torbers/shepherd_mix/brand/kh-24eva1117.png

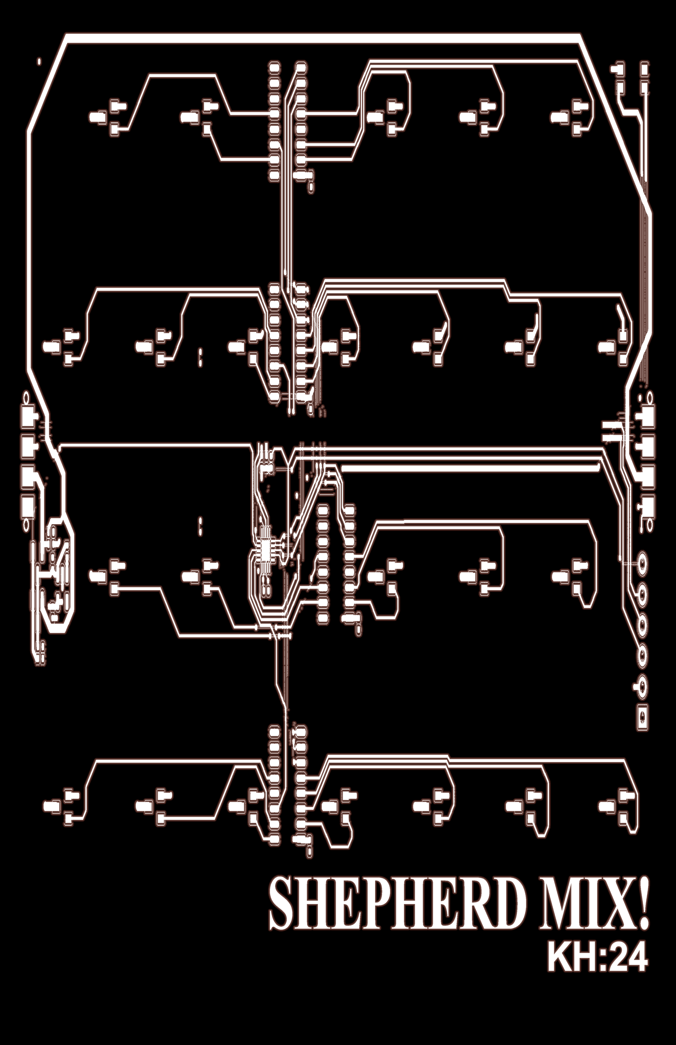
brand/kh-24eva1117.png
