torbers/shepherd_mix/brand/kh-24eva1117_v_one.png

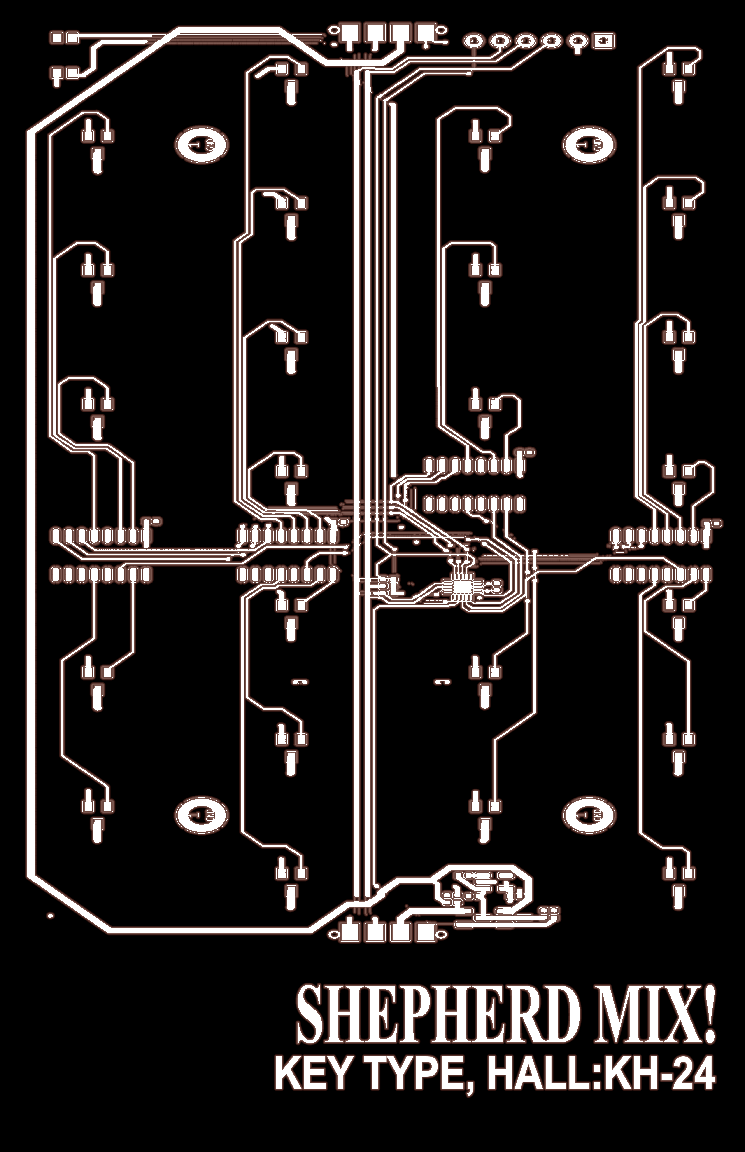
brand/kh-24eva1117_v_one.png
