torbers/shepherd_mix/brand/xray/1.jpg

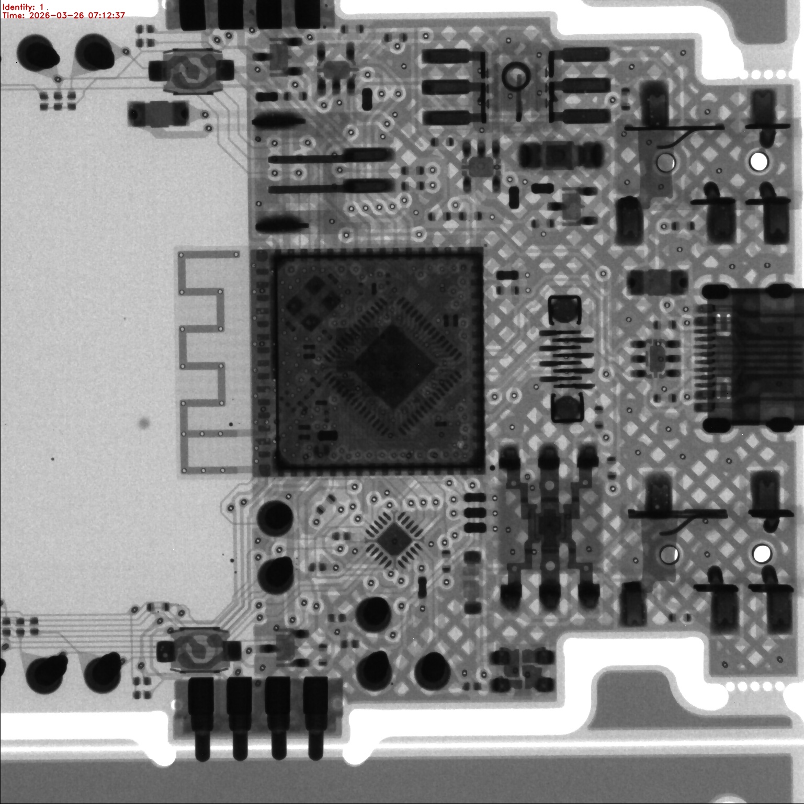
brand/xray/1.jpg
