torbers/shepherd_mix/brand/xray/2.jpg

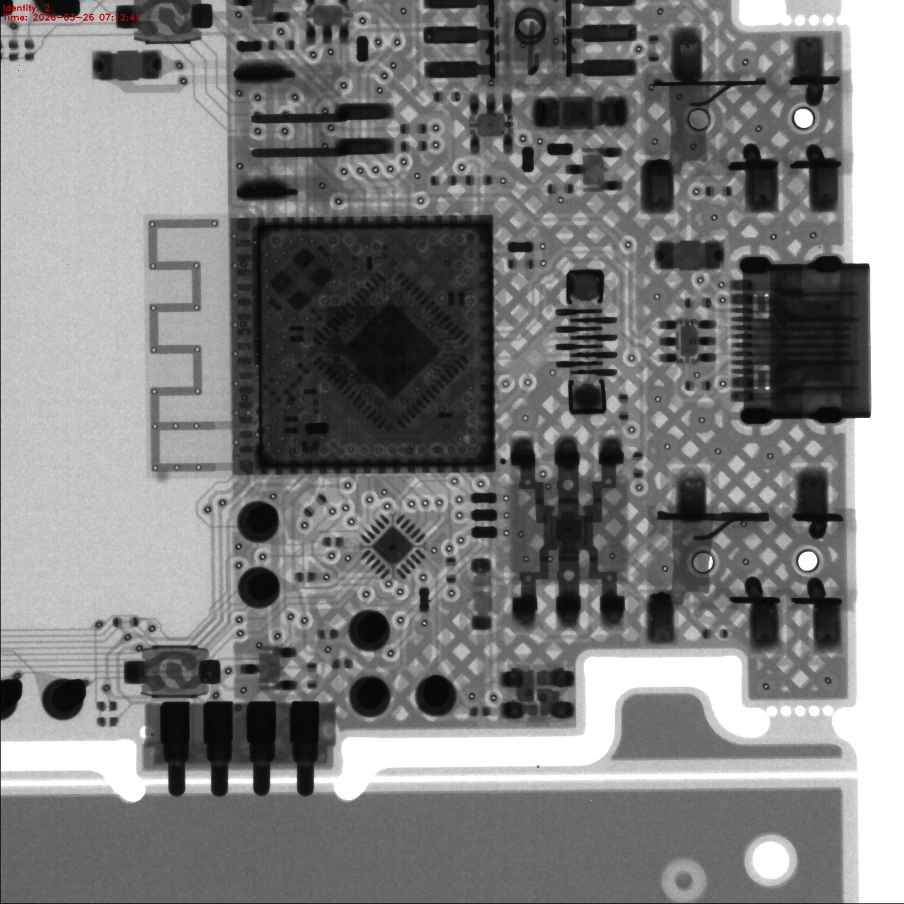
brand/xray/2.jpg
