torbers/shepherd_mix/brand/xray/5.jpg

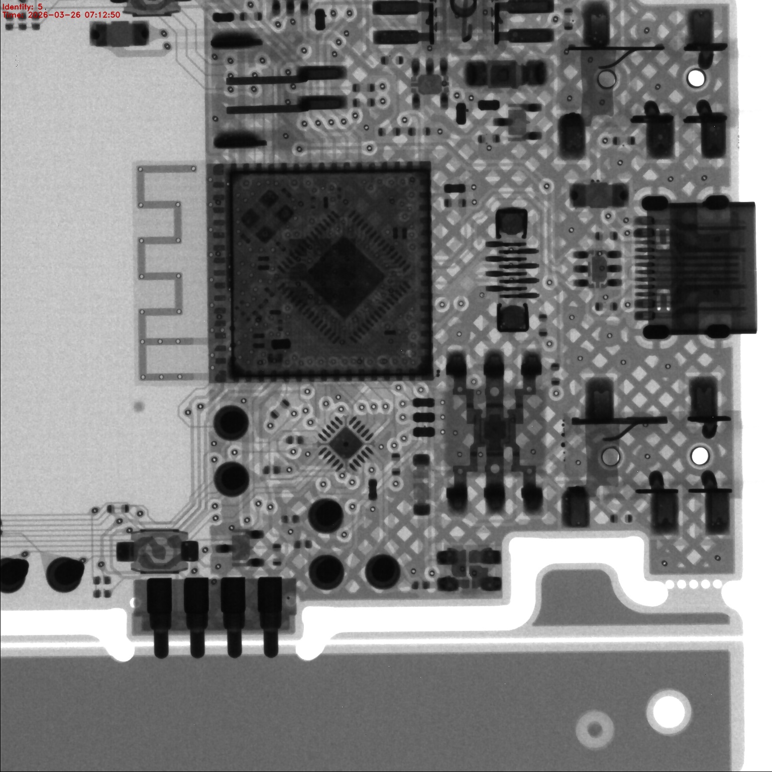
brand/xray/5.jpg
