torbers/shepherd_mix/kh-24 hall/hall face/ogd.png

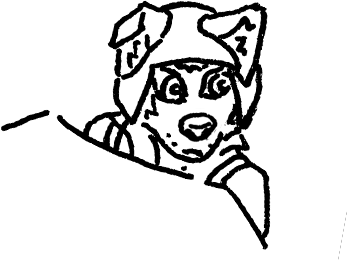
kh-24 hall/hall face/ogd.png
