torbers/shepherd_mix/kh-24 hall/hall_main_front2.png

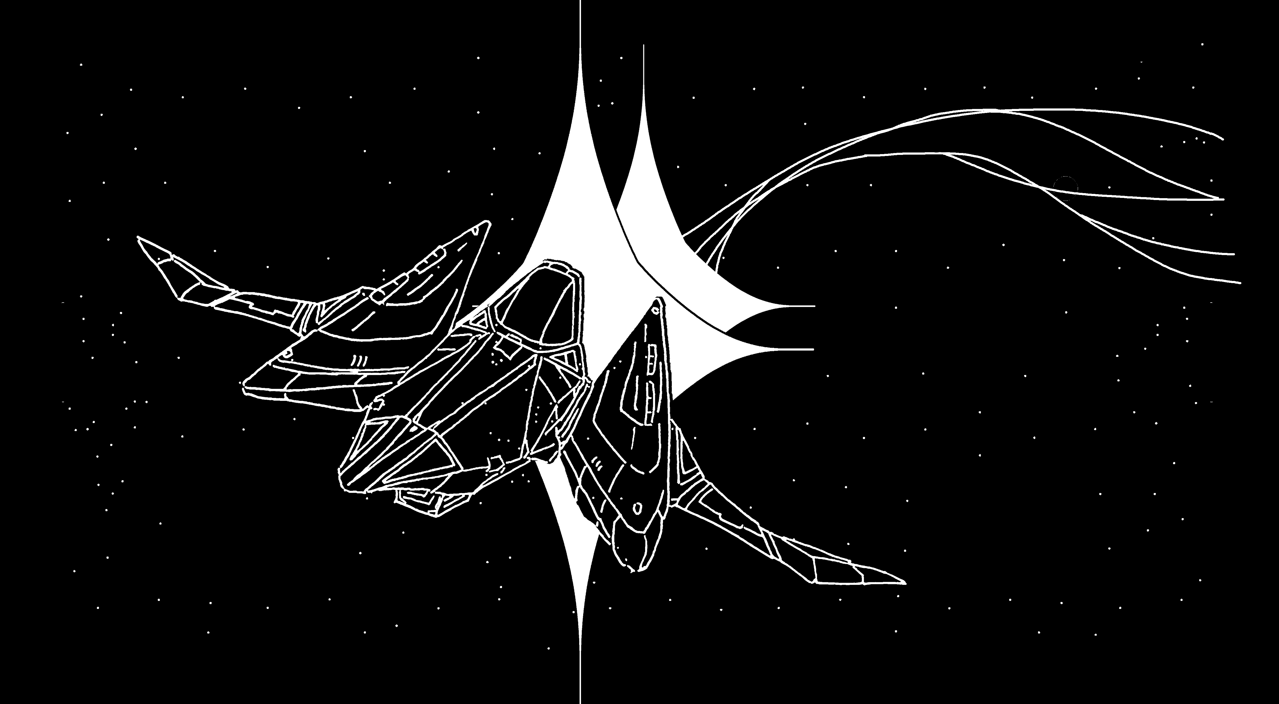
kh-24 hall/hall_main_front2.png
