torbers/shepherd_mix/kt-05 ctrl/dog2.png

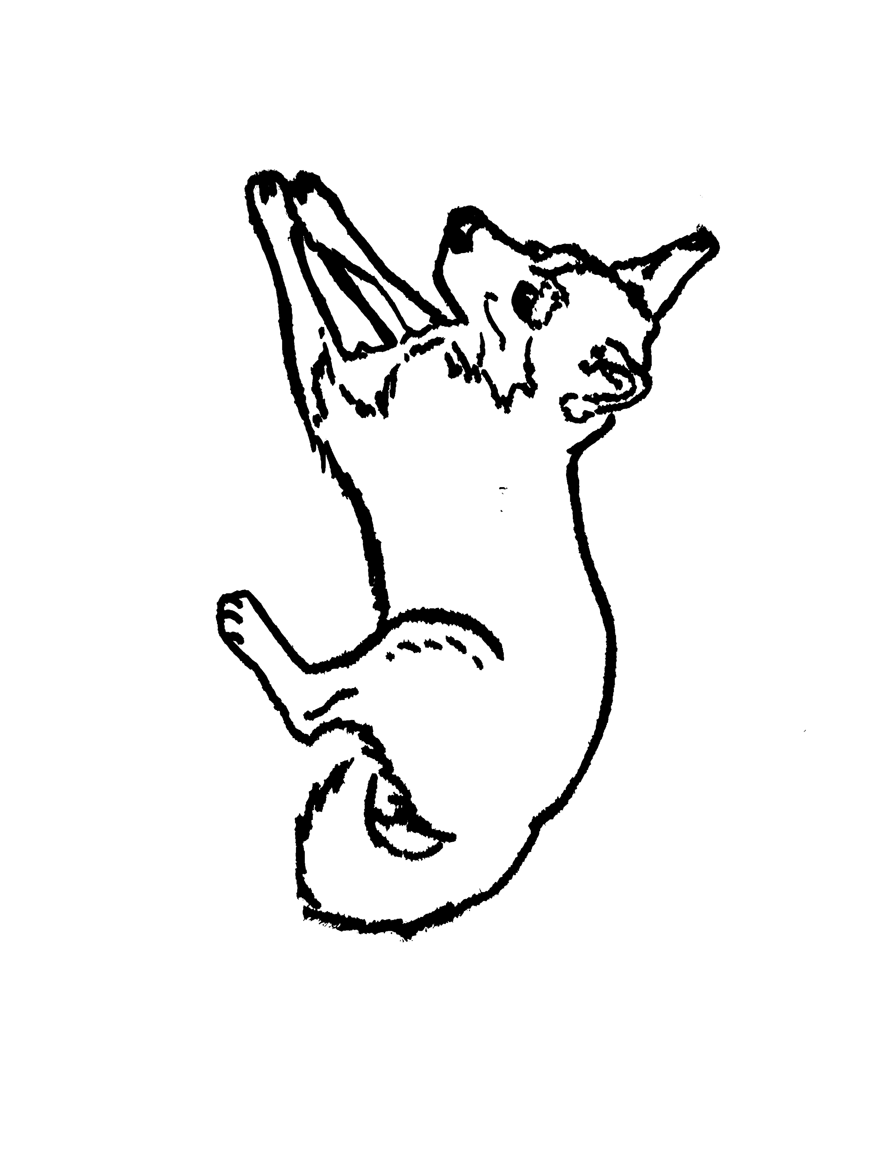
kt-05 ctrl/dog2.png
