torbers/shepherd_mix/kt-05 ctrl/dog2head2.png

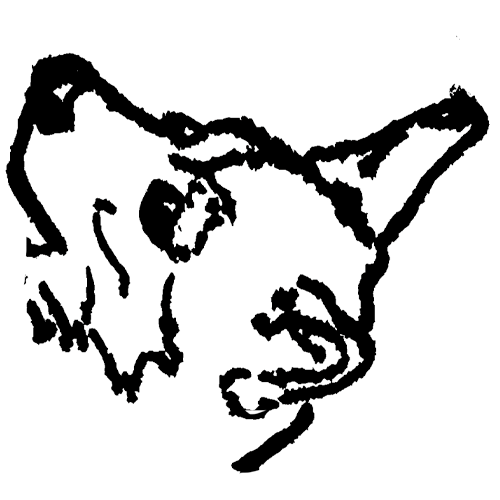
kt-05 ctrl/dog2head2.png
