torbers/shepherd_mix/kt-05 ctrl/dog2head.png

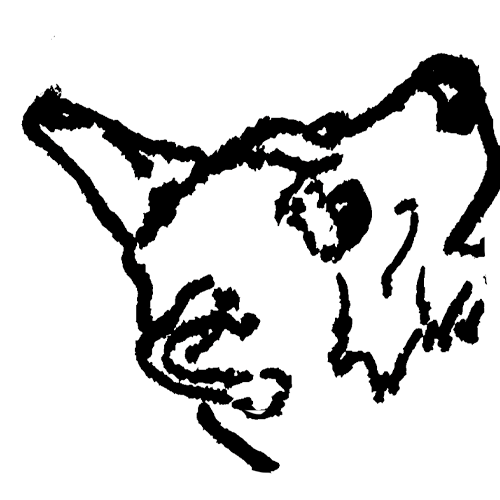
kt-05 ctrl/dog2head.png
