torbers/shepherd_mix/3d/CORE.step

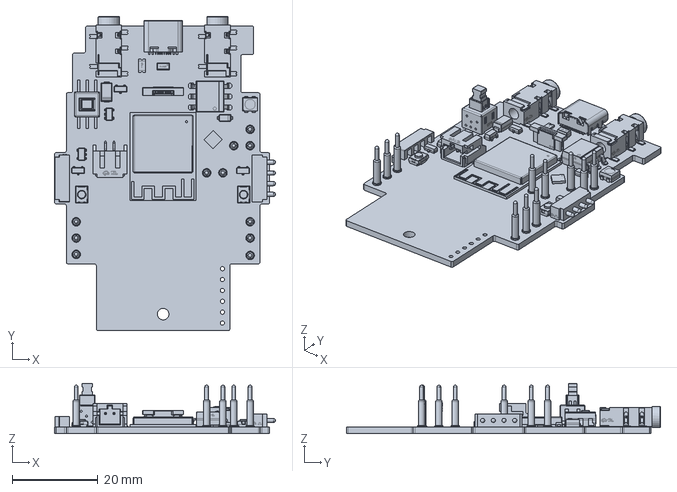
[picture p31: CAD file, 2026-03-25]
3d/CORE.step
51.7 x 73.4 x 11.7 mm
