torbers/shepherd_mix/pm0.1 core/arduino_src/core/core_wire_driver.h

#pragma once

#include <Arduino.h>
#include <Wire.h>
#include "modules.h"
#include "midi_mgmt.h"
#include "screen_update.h"

#define WIRE_CLOCK 4000000

#define MAX_MODULE_COUNT 16

class CoreWireDriver {
  public:
    // Module-to-module comm
    uint8_t BeginningAddress = 0x08;
    uint8_t NextNewAddress = BeginningAddress + 0x1;
    uint8_t I2CBus = 0;

    Module* Chain[MAX_MODULE_COUNT];
    TwoWire* Wire;
    MidiMgmt* MidiCall;

    uint8_t ModuleCount;

    bool begin(uint8_t wire_sda, uint8_t wire_scl, uint32_t wire_clock);
    uint8_t setControlRegVariable(uint8_t address, uint8_t register_address, uint8_t new_value);
    uint8_t findNextNewModule();

    //uint8_t updateModules();

    CoreWireDriver(TwoWire& wire_arg, MidiMgmt& midi_arg);
};
